kovesdy/portable-cell-initiative/4nec2/output/pci-downlink-30m_3dplot.bmp

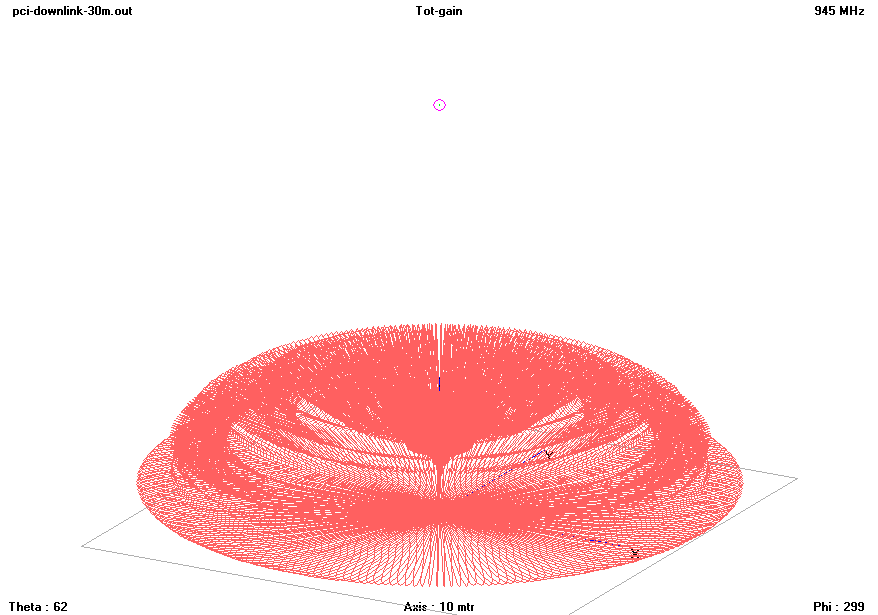
4nec2/output/pci-downlink-30m_3dplot.bmp
