kovesdy/portable-cell-initiative/4nec2/output/pci-downlink-30m_properties.bmp

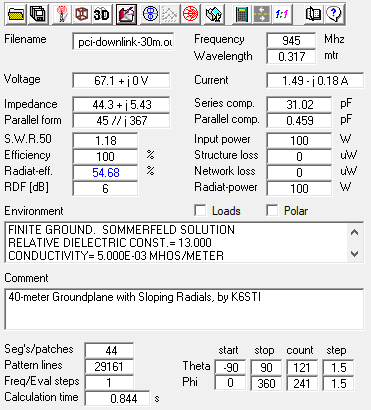
4nec2/output/pci-downlink-30m_properties.bmp
