kovesdy/portable-cell-initiative/4nec2/output/pci_downlink30m_radpattern.bmp

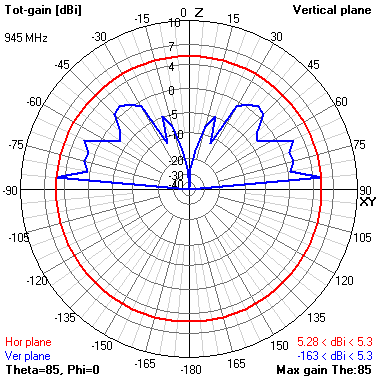
4nec2/output/pci_downlink30m_radpattern.bmp
