kovesdy/portable-cell-initiative/antenna_EM_modeling/pci_uplink02.bmp

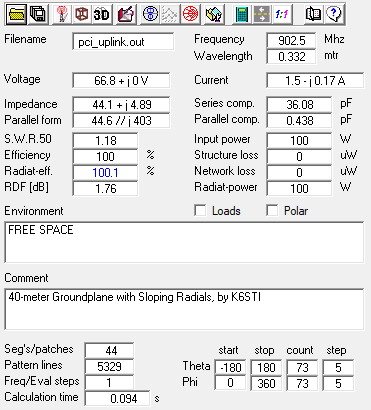
antenna_EM_modeling/pci_uplink02.bmp
