kovesdy/portable-cell-initiative/antenna_EM_modeling/pci_uplink30maboveearth.bmp

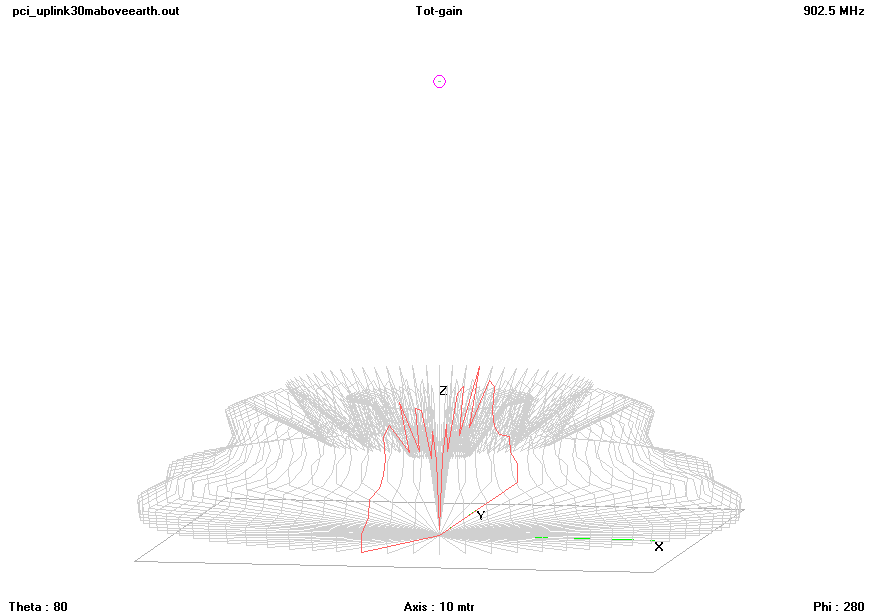
antenna_EM_modeling/pci_uplink30maboveearth.bmp
