kovesdy/portable-cell-initiative/antenna_EM_modeling/pci_uplink-geom.bmp

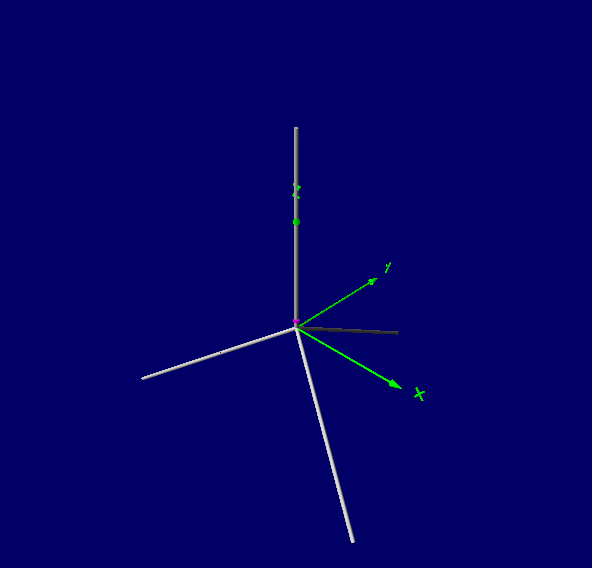
antenna_EM_modeling/pci_uplink-geom.bmp
