kovesdy/portable-cell-initiative/antenna_EM_modeling/pci_uplink.bmp

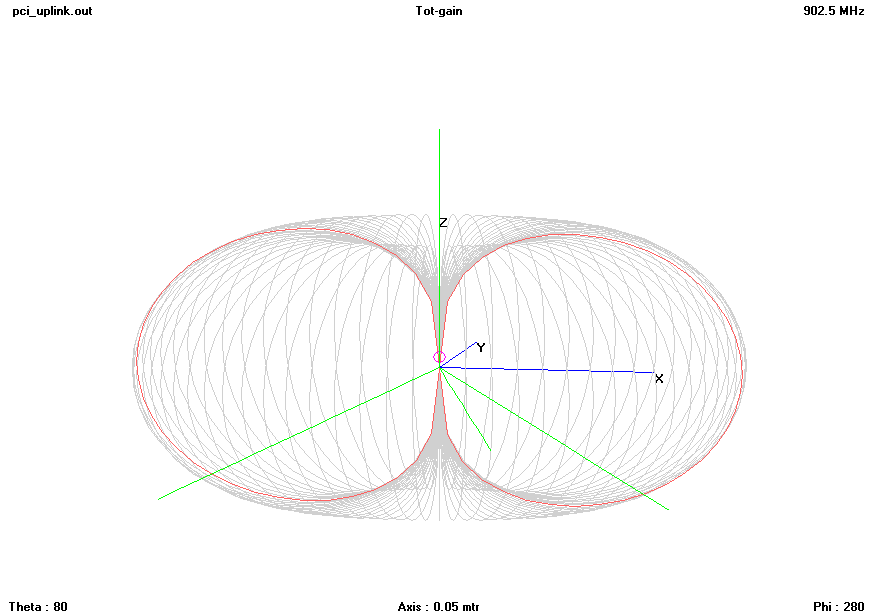
antenna_EM_modeling/pci_uplink.bmp
