kovesdy/portable-cell-initiative/structural_CAD/20180607_144912.jpg

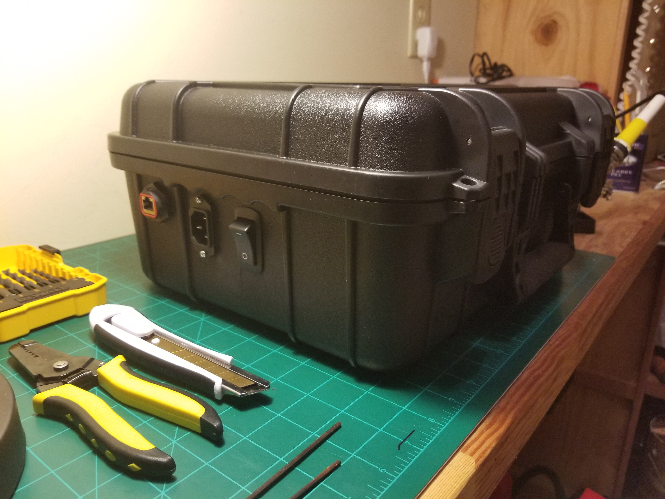
structural_CAD/20180607_144912.jpg
