kovesdy/portable-cell-initiative/structural_CAD/img/antenna_assembly-1.jpg

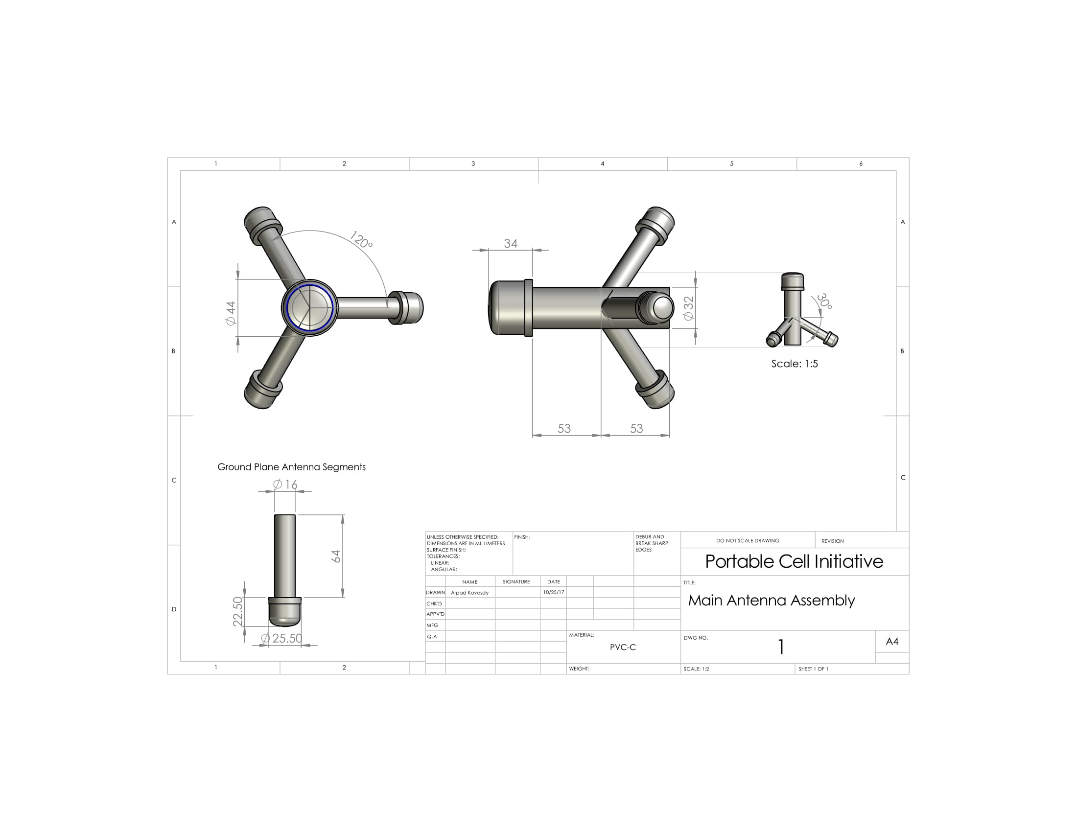
structural_CAD/img/antenna_assembly-1.jpg
