kovesdy/portable-cell-initiative/structural_CAD/20180324_205921.jpg

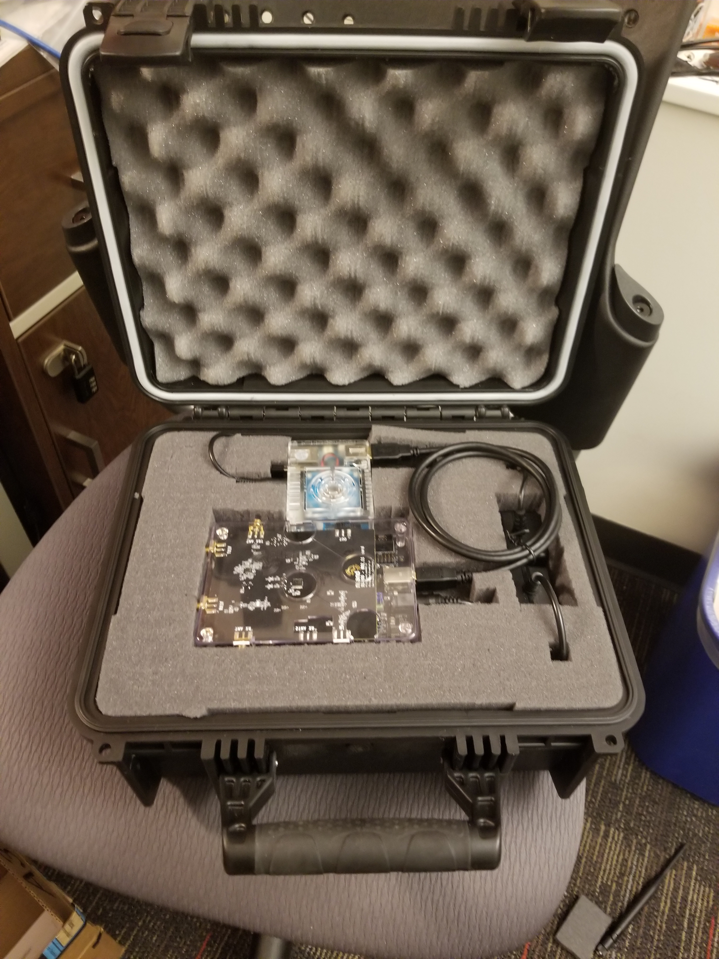
structural_CAD/20180324_205921.jpg
